Slynyr/ESP32-Walkie-Talkie-/MainLoop/Sprites.h

#ifndef SPRITES_H
#define SPRITES_H
#include <Arduino.h>

// 'Battery Icon', 13x13px
const unsigned char batteryBitmap [] PROGMEM = {
  0x00, 0x00, 0x00, 0x00, 0x00, 0x00, 0x7f, 0xe0, 0x40, 0x20, 0x40, 0x30, 0x40, 0x30, 0x40, 0x30,
  0x40, 0x20, 0x7f, 0xe0, 0x00, 0x00, 0x00, 0x00, 0x00, 0x00
};

// 'Node Connection Established', 13x13px
const unsigned char nodeConnectionEstablished [] PROGMEM = {
  0x00, 0x00, 0x00, 0x00, 0x1f, 0xc0, 0x7f, 0xf0, 0xf0, 0x78, 0x4f, 0x90, 0x1f, 0xc0, 0x18, 0xc0,
  0x07, 0x00, 0x07, 0x00, 0x02, 0x00, 0x00, 0x00, 0x00, 0x00
};

// 'Node Connection Failed Icon', 13x13px
const unsigned char noNodeConnectionmap [] PROGMEM = {
  0x00, 0x00, 0x02, 0x00, 0x02, 0x00, 0x3f, 0xe0, 0x7a, 0xf0, 0xe2, 0x38, 0x1a, 0xc0, 0x18, 0xc0,
  0x02, 0x00, 0x07, 0x00, 0x07, 0x00, 0x00, 0x00, 0x00, 0x00
};

// 'Nodelogo', 128x48px
const unsigned char splashNodeLogo [] PROGMEM = {
  0xff, 0xff, 0xff, 0xff, 0xff, 0xff, 0xff, 0xff, 0xff, 0xff, 0xff, 0xff, 0xff, 0xff, 0xff, 0xff,
  0xff, 0xff, 0xff, 0xff, 0xff, 0xff, 0xff, 0xff, 0xff, 0xff, 0xff, 0xff, 0xff, 0xff, 0xff, 0xff,
  0xff, 0xff, 0xff, 0xff, 0xff, 0xff, 0xff, 0xf0, 0xff, 0xff, 0xff, 0xff, 0xff, 0xff, 0xff, 0xff,
  0xff, 0xff, 0xff, 0xff, 0xff, 0xff, 0xff, 0xe0, 0x7f, 0xff, 0xff, 0xff, 0xff, 0xff, 0xff, 0xff,
  0xff, 0xff, 0xff, 0xff, 0xff, 0xff, 0xff, 0xc0, 0x3f, 0xff, 0xff, 0xff, 0xff, 0xff, 0xff, 0xff,
  0xff, 0xff, 0xff, 0xff, 0xff, 0xff, 0xff, 0x80, 0x1f, 0xff, 0xff, 0xff, 0xff, 0xff, 0xff, 0xff,
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
  0x00, 0x0f, 0xf0, 0x0f, 0xf1, 0xfe, 0x01, 0xfe, 0x7f, 0x80, 0x7f, 0x8f, 0xf0, 0x1f, 0xf0, 0x00,
  0x00, 0x0f, 0xf0, 0x0f, 0xf1, 0xfe, 0x01, 0xfe, 0x7f, 0x80, 0x7f, 0x8f, 0xf0, 0x0f, 0xf0, 0x00,
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
};

#endif
