Slynyr/ESP32-Walkie-Talkie-/MainLoop/ExternalIO.cpp

//This file is namely for external inputs like buttons NOT I2S devices like the mic and speaker
#include "ExternalIO.h"


//Pin declare
byte batteryMonitorPin = 34;
byte debugPushButtonPin = 5;
byte upButtonPin = 5;
byte downButtonPin = 19;
byte modeButtonPin = 26;
byte talkButtonPin = 27;
byte extraButtonPin = 35;

//Initialize structure
interfaceButtons buttons[5];

//timing
const int longPressThreshhold = 250;  //ms
int prevMillisUp = 0;
int prevMillisDown = 0;

//states
bool isUpButtonPushed = false;
bool isDownButtonPushed = false;

void inputsInitialize() {
  pinMode(batteryMonitorPin, ANALOG);
  pinMode(debugPushButtonPin, INPUT_PULLUP);
  pinMode(upButtonPin, INPUT_PULLUP);
  pinMode(downButtonPin, INPUT_PULLUP);
  pinMode(modeButtonPin, INPUT_PULLUP);
  pinMode(talkButtonPin, INPUT_PULLUP);
  pinMode(extraButtonPin, INPUT_PULLUP);

  //Button pin declare for struct
  /*  0: up = 5
      1: down = 19
      2: mode = 26
      3: talk = 27
      4: extra = 35
  */
  buttons[0].buttonPin = 5;
  buttons[1].buttonPin = 19;
  buttons[2].buttonPin = 26;
  buttons[3].buttonPin = 27;
  buttons[4].buttonPin = 35;
}

unsigned short int pollBattery() {
  unsigned short int batteryLevelRaw;
  batteryLevelRaw = analogRead(batteryMonitorPin);

  return batteryLevelRaw;
}

void pushButtonState() {
  unsigned long pressDuration = 0;

  for (int i = 0; i <= 4; i++) {
    // 0 is unpressed, 1 is pressed
    buttons[i].currentState = digitalRead(buttons[i].buttonPin);
    if (buttons[i].previousState == LOW && buttons[i].currentState == HIGH) {  //Button pressed
      buttons[i].timePressed = millis();  //Log pressed time
      buttons[i].samePress = true;

    } else if (buttons[i].previousState == HIGH && buttons[i].currentState == LOW) {  //Button released
      buttons[i].timeReleased = millis();                                             //Log released time
      buttons[i].samePress = false;

      pressDuration = buttons[i].timeReleased - buttons[i].timePressed;  //Pressed duration is these times subtracted

      if (pressDuration <= SHORT_PRESS_TIME) {
        buttons[i].pressStatus = "SHORT";
        //Serial.printf("[UPDATE] Updated button %d press status to SHORT", i);
      }

    } else if (buttons[i].previousState == HIGH && buttons[i].currentState == HIGH) {

      if (millis() - buttons[i].timePressed >= SHORT_PRESS_TIME) {
        buttons[i].pressStatus = "LONG";
      }
      
    } else {
      //If function hasn't initialized
      buttons[i].samePress = false;
      buttons[i].pressStatus = NULL;
      buttons[i].previousState = LOW;
    }
    buttons[i].previousState = buttons[i].currentState;
  }
}

bool rawPushButton() {
  return digitalRead(debugPushButtonPin);
}

void ioUpdate() {
  pushButtonState();
}
